khinds10/QuickInternetClock/src/settings-default.h

// WiFi credentials
const char* ssid = "LINKSYS";
const char* password = "password";

// NTP setup
const char* ntpServer = "north-america.pool.ntp.org";
const long  gmtOffset_sec = -18000; // Eastern Daylight Time (EDT)
const int   daylightOffset_sec = 3600;
